bastijnvandenboom/Stereotaxic_motorized_arm/images/BB_Stereotaxic_Robot6.jpg

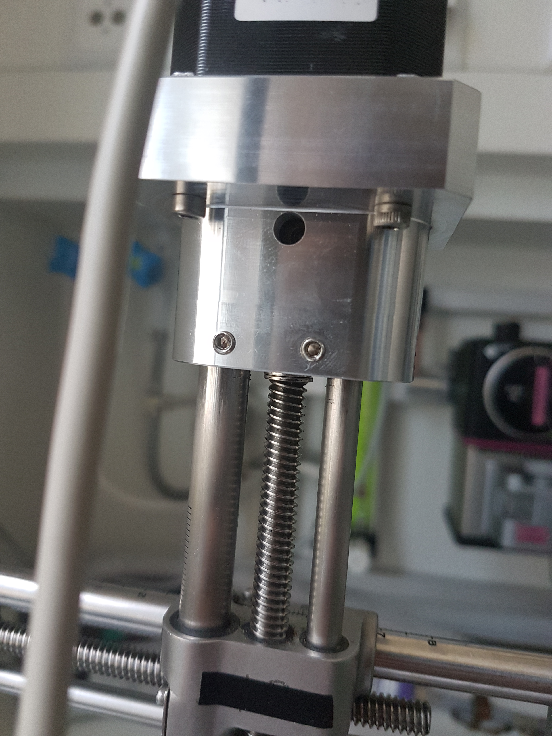
images/BB_Stereotaxic_Robot6.jpg
